David-EIPI/esp32-zigbee-light-mini/images/20250422_165926.JPG

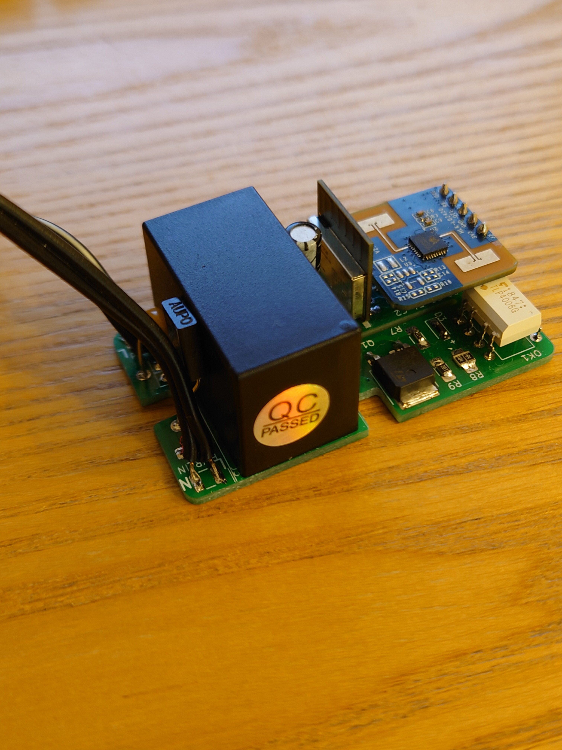
images/20250422_165926.JPG
