David-EIPI/esp32-zigbee-light-mini/images/20250422_170016.JPG

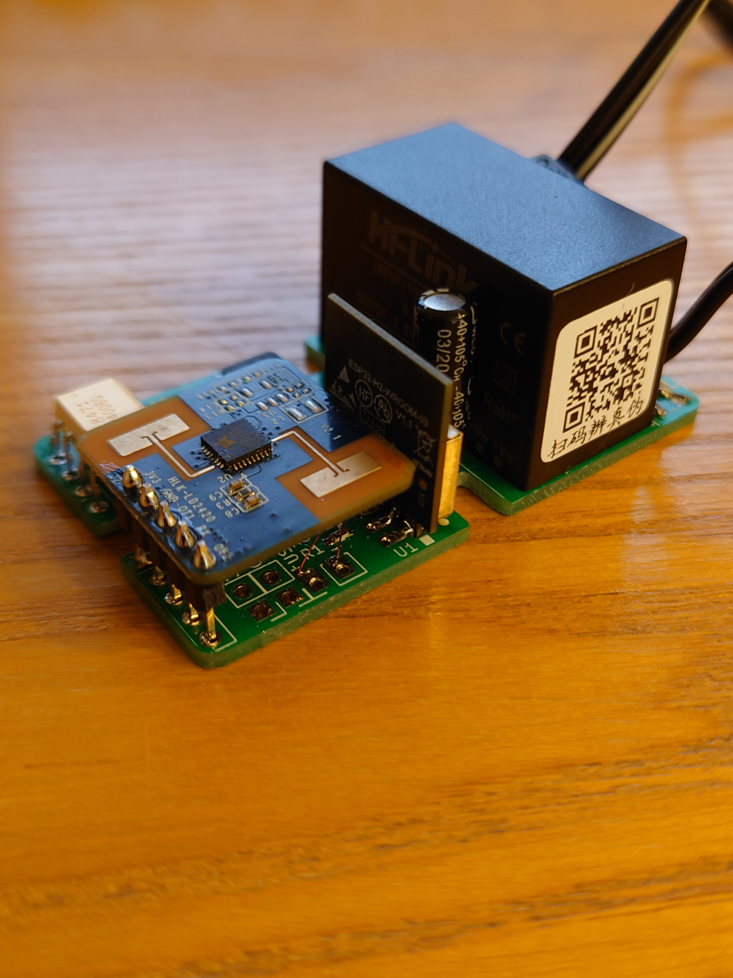
images/20250422_170016.JPG
