David-EIPI/esp32-zigbee-light-mini/firmware/main/light_driver.c

/*
 * SPDX-FileCopyrightText: 2021-2023 Espressif Systems (Shanghai) CO LTD
 *
 * SPDX-License-Identifier: LicenseRef-Included
 *
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
 * 3. Neither the name of the copyright holder nor the names of its contributors
 *    may be used to endorse or promote products derived from this software without
 *    specific prior written permission.
 *
 * 4. Any software provided in binary form under this license must not be reverse
 *    engineered, decompiled, modified and/or disassembled.
 *
 * THIS SOFTWARE IS PROVIDED BY THE COPYRIGHT HOLDERS AND CONTRIBUTORS "AS IS"
 * AND ANY EXPRESS OR IMPLIED WARRANTIES, INCLUDING, BUT NOT LIMITED TO, THE
 * IMPLIED WARRANTIES OF MERCHANTABILITY AND FITNESS FOR A PARTICULAR PURPOSE
 * ARE DISCLAIMED. IN NO EVENT SHALL THE COPYRIGHT HOLDER OR CONTRIBUTORS BE
 * LIABLE FOR ANY DIRECT, INDIRECT, INCIDENTAL, SPECIAL, EXEMPLARY, OR
 * CONSEQUENTIAL DAMAGES (INCLUDING, BUT NOT LIMITED TO, PROCUREMENT OF
 * SUBSTITUTE GOODS OR SERVICES; LOSS OF USE, DATA, OR PROFITS; OR BUSINESS
 * INTERRUPTION) HOWEVER CAUSED AND ON ANY THEORY OF LIABILITY, WHETHER IN
 * CONTRACT, STRICT LIABILITY, OR TORT (INCLUDING NEGLIGENCE OR OTHERWISE)
 * ARISING IN ANY WAY OUT OF THE USE OF THIS SOFTWARE, EVEN IF ADVISED OF THE
 * POSSIBILITY OF SUCH DAMAGE.
 */

#include "esp_log.h"
#include "led_strip.h"
#include "light_driver.h"

static led_strip_handle_t s_led_strip;
static uint16_t s_red = 255, s_green = 255, s_blue = 255;

void light_driver_set_power(uint8_t power)
{
    ESP_ERROR_CHECK(led_strip_set_pixel(s_led_strip, 0, (s_red * power) / 255, (s_green * power) / 255, (s_blue * power) / 255));
    ESP_ERROR_CHECK(led_strip_refresh(s_led_strip));
}

void light_driver_init(bool power)
{
    led_strip_config_t led_strip_conf = {
        .max_leds = CONFIG_EXAMPLE_STRIP_LED_NUMBER,
        .strip_gpio_num = CONFIG_EXAMPLE_STRIP_LED_GPIO,
    };
    led_strip_rmt_config_t rmt_conf = {
        .resolution_hz = 10 * 1000 * 1000, // 10MHz
    };
    ESP_ERROR_CHECK(led_strip_new_rmt_device(&led_strip_conf, &rmt_conf, &s_led_strip));
    light_driver_set_power(power);
}
