David-EIPI/esp32-zigbee-light-mini/firmware/main/ld2420_comm.h

#pragma once

#include <stdint.h>




extern volatile int32_t motionThreshold;
extern volatile int motionDetected;
extern volatile uint32_t ld2420_Distance;
extern volatile int32_t calibrationTime;

void ld2420_task(void *arg);
